joaco05/Rover2022/Despiece/Fotos/20220425_215843.jpg

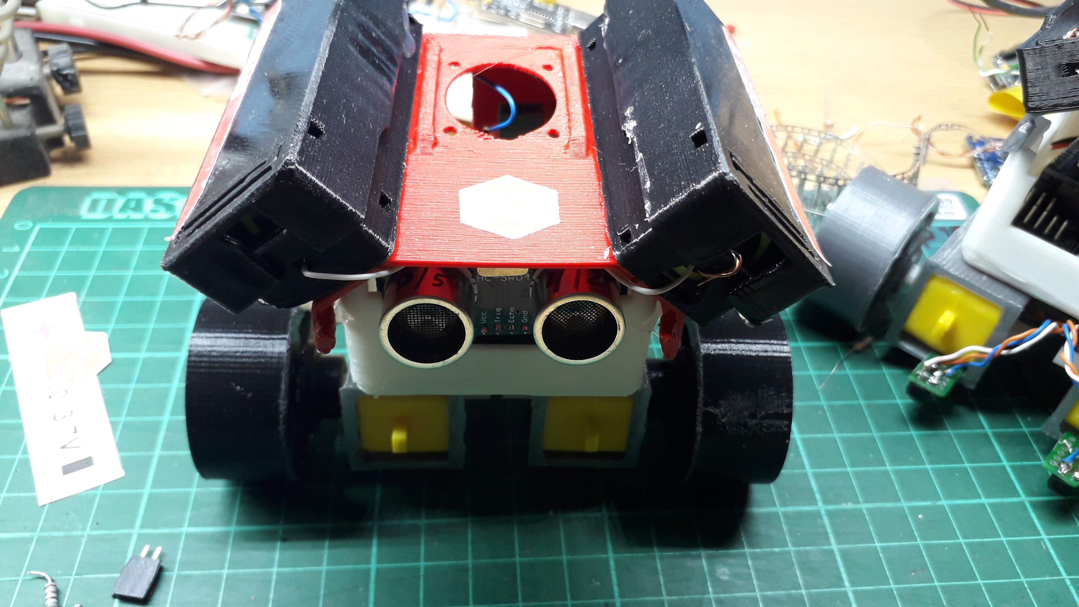
Despiece/Fotos/20220425_215843.jpg
