joaco05/Rover2022/Despiece/capture_001_17042022_132419.jpg

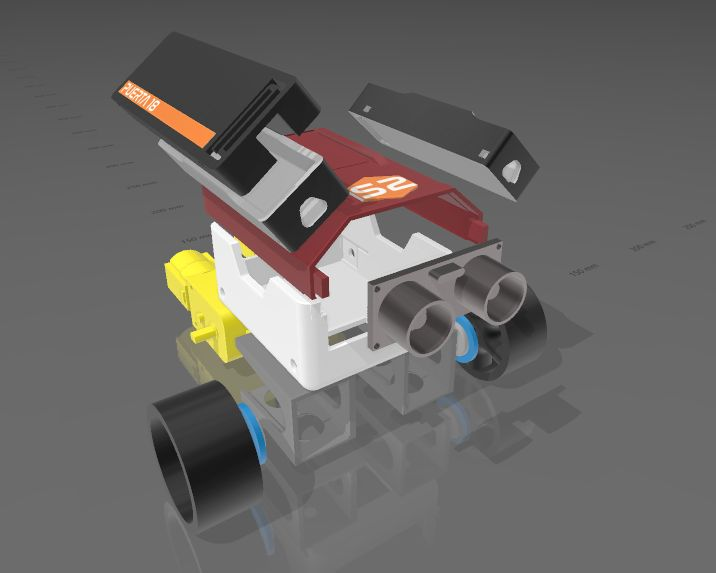
Despiece/capture_001_17042022_132419.jpg
