joaco05/Rover2022/Despiece/capture_003_17042022_132510.jpg

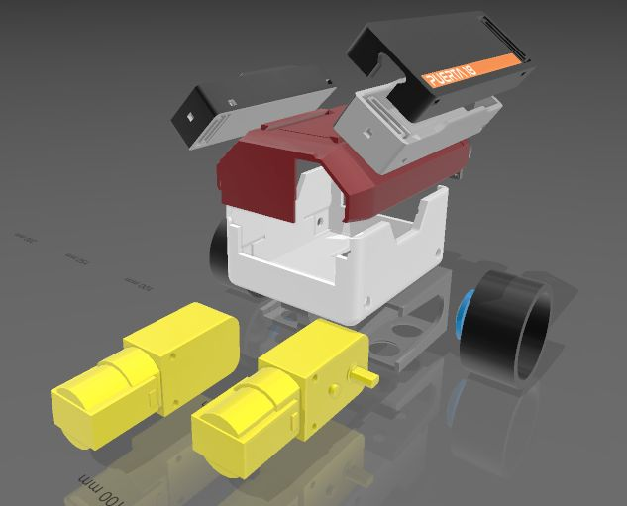
Despiece/capture_003_17042022_132510.jpg
