joaco05/Rover2022/Despiece/capture_004_17042022_132556.jpg

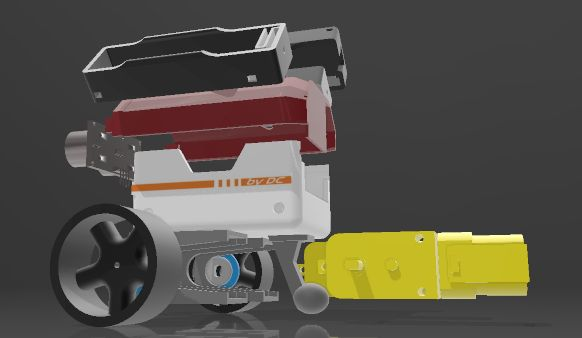
Despiece/capture_004_17042022_132556.jpg
