joaco05/Rover2022/Despiece/Fotos/MotorDriver.jpg

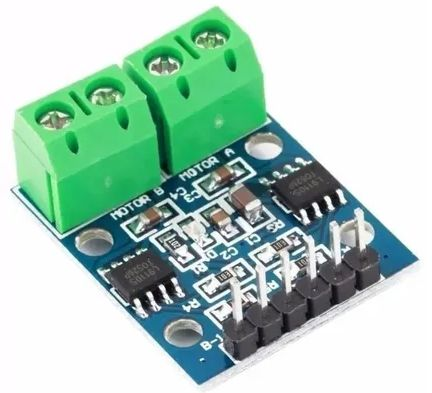
Despiece/Fotos/MotorDriver.jpg
