joaco05/Rover2022/Electronica/HCOPTO0064_BasicCharacteristics.png

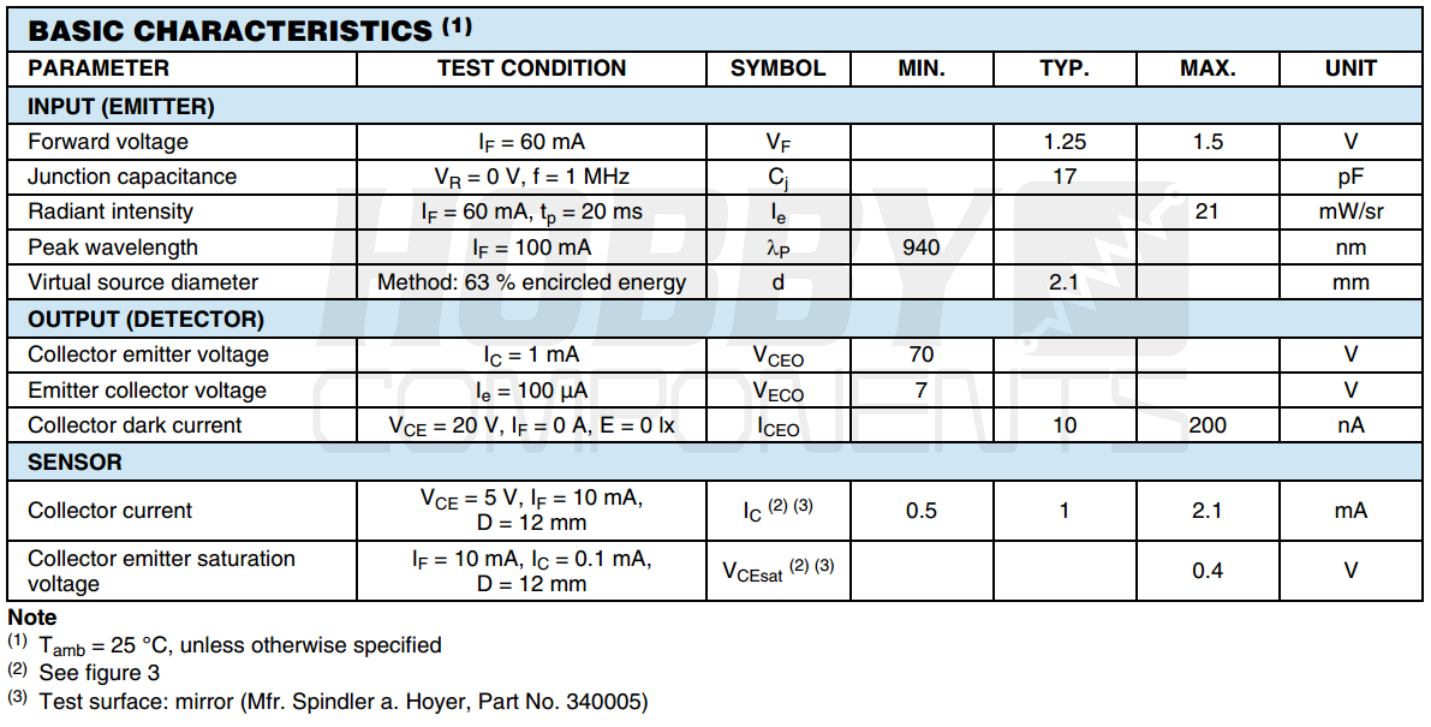
Electronica/HCOPTO0064_BasicCharacteristics.png
